OLIMEX/ESP32-SBC-FabGL/HARDWARE/Hardware-revision-B/3d/DO-214AC_SMA.step

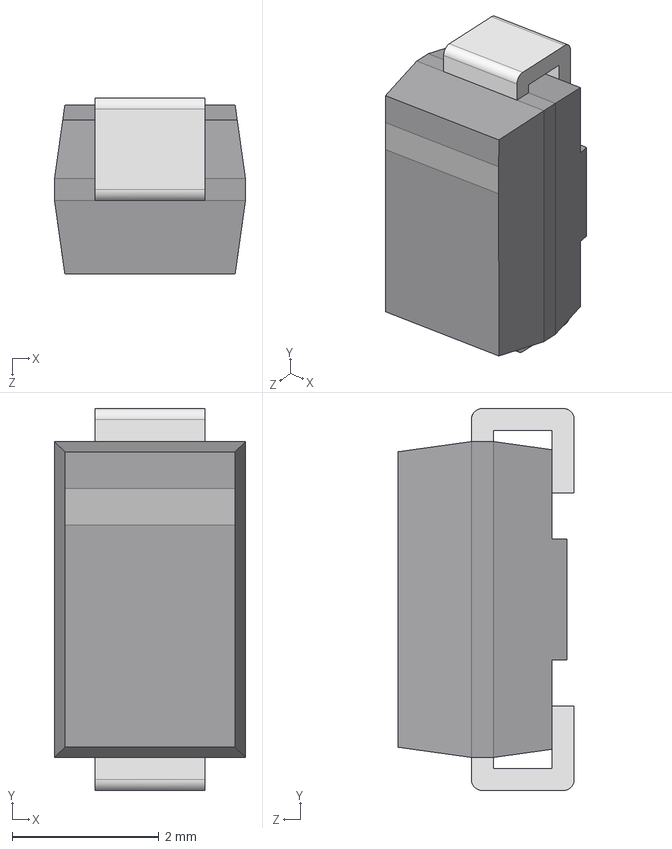
[picture p22: CAD file, 2023-07-04]
HARDWARE/Hardware-revision-B/3d/DO-214AC_SMA.step
2.60 x 5.20 x 2.40 mm
