OLIMEX/ESP32-SBC-FabGL/HARDWARE/Hardware-revision-B/3d/HN1x2-PinHeader_1x02_P2.54mm_Vertical.step

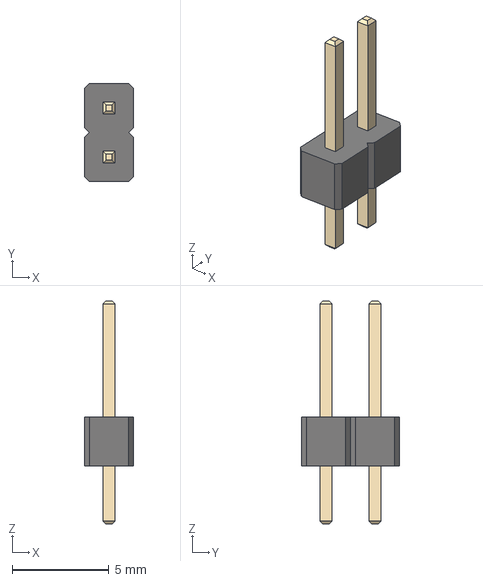
[picture p23: CAD file, 2023-07-04]
HARDWARE/Hardware-revision-B/3d/HN1x2-PinHeader_1x02_P2.54mm_Vertical.step
2.54 x 5.08 x 11.5 mm
