OLIMEX/ESP32-SBC-FabGL/HARDWARE/Hardware-revision-B/3d/ESP32-WROVER-I-56544.STEP

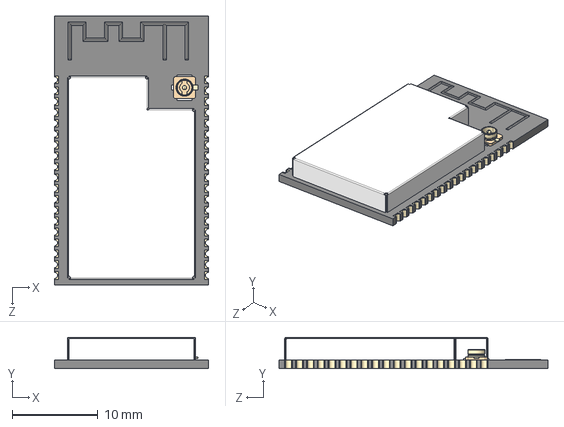
[picture p24: CAD file, 2023-07-04]
HARDWARE/Hardware-revision-B/3d/ESP32-WROVER-I-56544.STEP
18.0 x 3.65 x 31.4 mm
