OLIMEX/ESP32-SBC-FabGL/HARDWARE/Hardware-revision-B/3d/SOT-23.step

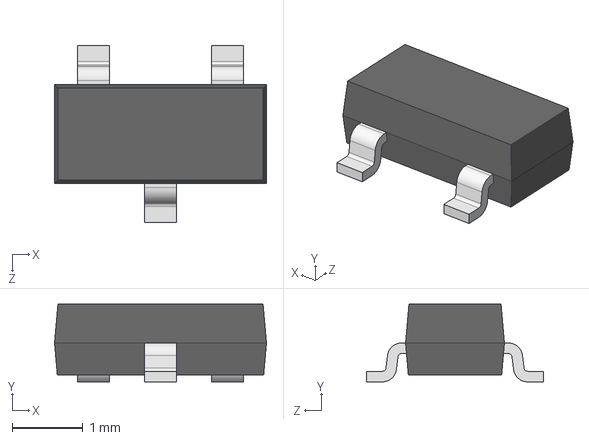
[picture p25: CAD file, 2023-07-04]
HARDWARE/Hardware-revision-B/3d/SOT-23.step
3.00 x 1.10 x 2.50 mm
