OLIMEX/ESP32-SBC-FabGL/HARDWARE/Hardware-revision-B/3d/HN1x12-PinHeader_1x12_P2.54mm_Vertical.step

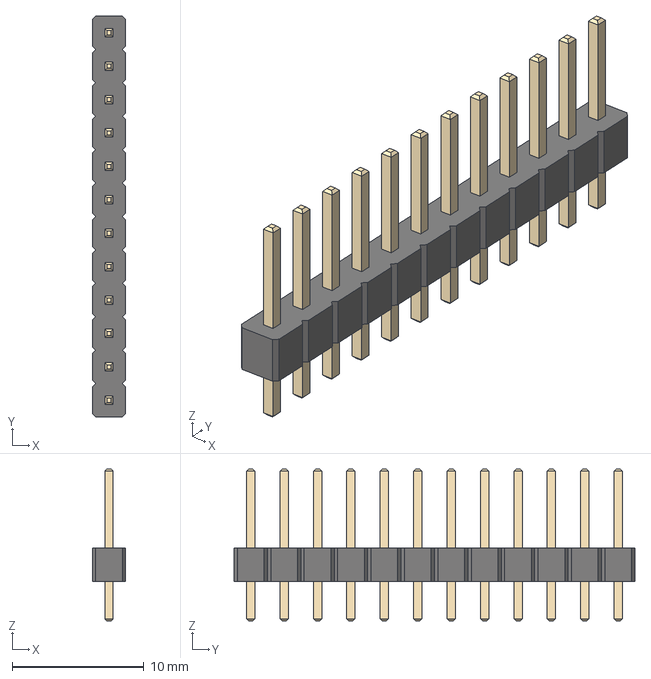
[picture p26: CAD file, 2023-07-04]
HARDWARE/Hardware-revision-B/3d/HN1x12-PinHeader_1x12_P2.54mm_Vertical.step
2.54 x 30.5 x 11.5 mm
