OLIMEX/ESP32-SBC-FabGL/HARDWARE/Hardware-revision-B/3d/Header_right_angle_10way(2x5).step

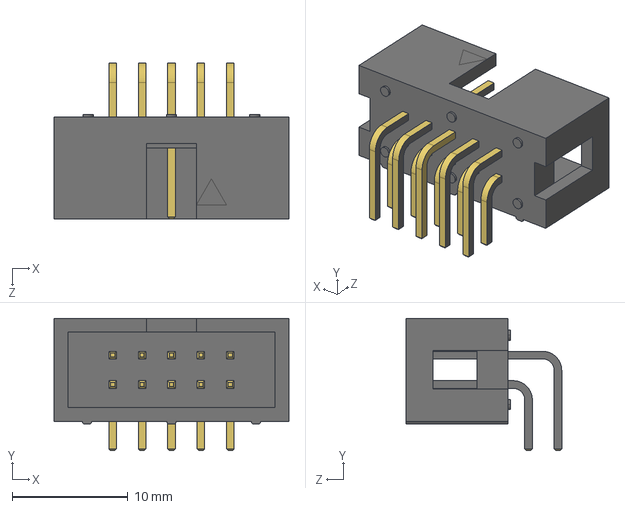
[picture p27: CAD file, 2023-07-04]
HARDWARE/Hardware-revision-B/3d/Header_right_angle_10way(2x5).step
20.3 x 11.4 x 13.4 mm
