OLIMEX/ESP32-SBC-FabGL/HARDWARE/Hardware-revision-B/3d/MSOP10-1.step

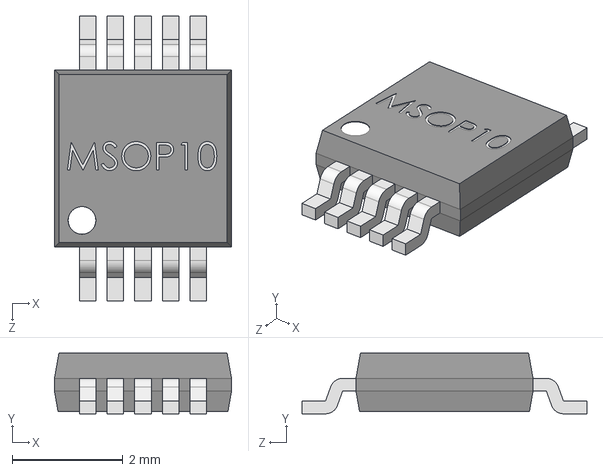
[picture p28: CAD file, 2023-07-04]
HARDWARE/Hardware-revision-B/3d/MSOP10-1.step
3.20 x 1.10 x 5.15 mm
