OLIMEX/ESP32-SBC-FabGL/HARDWARE/Hardware-revision-B/3d/Audio_Jack-3.5mm---CUI_SJ1-3515-SMT-TR.step

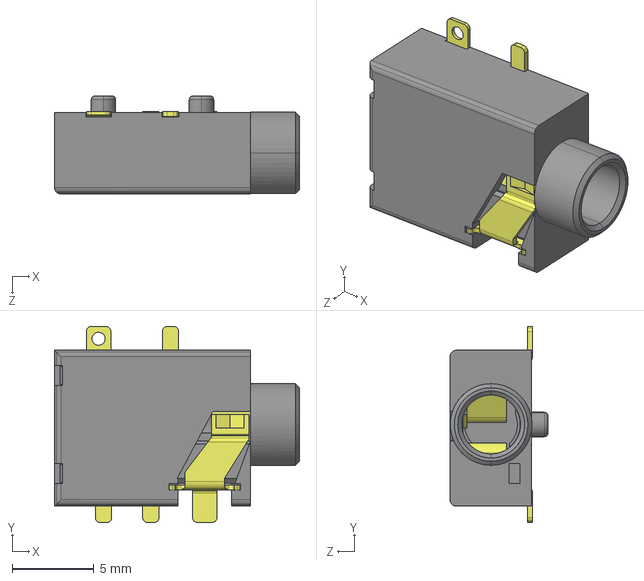
[picture p29: CAD file, 2023-07-04]
HARDWARE/Hardware-revision-B/3d/Audio_Jack-3.5mm---CUI_SJ1-3515-SMT-TR.step
15.0 x 12.0 x 6.00 mm
