OLIMEX/ESP32-SBC-FabGL/HARDWARE/Hardware-revision-B/3d/User Library-SOT50P160X60-6.step

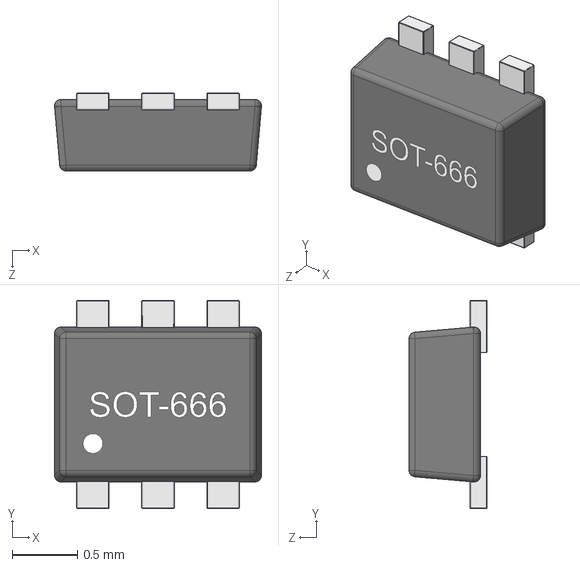
[picture p30: CAD file, 2023-07-04]
HARDWARE/Hardware-revision-B/3d/User Library-SOT50P160X60-6.step
1.59 x 1.60 x 0.6 mm
