OLIMEX/ESP32-SBC-FabGL/SOFTWARE/CH32V003_Driver/examples/ESP32-SBC-FabGL_UART_Bridge/ESP32-SBC-FabGL_UART_Bridge.ino

/**
 * @brief ESP32-SBC-FabGL UART bridge example
 * Tested with:
 * Board revision   : Rev.A
 * Arduino IDE      : 1.8.9
 * Espressif package: 2.0.9
 * 
 * Example description:
 * Example will check the version of the CH32V003 firmware expander
 * UART feature is not available before 1.0v
 * Recommended baudrate up to 115200. On higher values longer messages will cause malfunctions
 * 
 * If initialized and configured properly upon receiving a character
 * on the expander's RX it will be sent to ESP32's TX and vice versa.
 * To achieve that the when character is received on the expander's RX
 * IO_EXP_IRQ will be set (indicating an interrupt) and then the ESP32
 * will read it. When ESP32 receives a character it will be indicated
 * using Serial.available and then the characte will be sent to
 * expander's TX line.
 * 
*/

#include "CH32V003.h"

CH32V003 Expander;

void error(char message[])
{
  Serial.println(message);
  while (1);
}

void setup()
{
  Serial.begin(115200);

  if (Expander.begin ())
  {
    uint16_t ver = Expander.version();
    Serial.printf("CH32V003 firmware version: %d.%d" EOL, ver >> 8, ver & 0xFF);
    if (ver < 0x0100)
      error("Your CH32V003 firmware version does not support features needed by this example");
  }
  else
    error("CH32V003 not found");

  Expander.configureUART (115200, UART_StopBits_1, UART_Parity_No);

  pinMode (IO_EXP_IRQ, INPUT);
}

void loop()
{
  static uint8_t SendChar=0, ReceiveChar=0;
  if (Serial.available ())
  {
    SendChar = Serial.read ();
    Expander.writeUART (&SendChar, 1);
  }

  if (digitalRead(IO_EXP_IRQ))
  {
    Expander.readUART(&ReceiveChar, 1);
    Serial.print ((char)ReceiveChar);
  }
}
